willjschmitt/joulia-controller/update_test.py

"""Tests for the update module."""

import unittest

from testing.stub_joulia_webserver_client import StubJouliaHTTPClient
from update import GitUpdateManager


class StubRepo(object):
    """Stub object for a gitpython Repo object."""
    def __init__(self):
        self.head = StubHead()
        self.remotes = StubRemotes()
        self.git = StubGit()

    def commit(self, commit_hash):
        return StubCommit()


class StubHead(object):
    def __init__(self):
        self.object = StubObject()


class StubObject(object):
    def __init__(self):
        self.binsha = bytearray.fromhex('abcd'*10)


class StubRemotes(object):
    def __init__(self):
        self.origin = StubOrigin()


class StubOrigin(object):
    def fetch(self):
        pass


class StubCommit(object):
    pass


class StubGit(object):
    def checkout(self, commit):
        pass


def stub_system_restarter():
    """Fake function that just returns nothing to act like a "system restarter".
    """


class TestGitUpdateManager(unittest.TestCase):
    def setUp(self):
        self.repo = StubRepo()
        self.client = StubJouliaHTTPClient("http://fakehost")
        self.client.brewhouse = {
            'id': 1,
            'software_version': 9,
        }
        self.brewhouse_id = 1
        self.update_manager = GitUpdateManager(
            self.repo, self.client, self.brewhouse_id,
            system_restarter=stub_system_restarter)

    def test_check_version_no_new_version(self):
        self.client.latest_controller_release = {
            "id": 9,
            "commit_hash": "abcdabcdabcdabcdabcdabcdabcdabcdabcdabcd"}
        updated = self.update_manager._check_version()
        self.assertFalse(updated)

    def test_check_version_no_new_version_wrong_saved_id(self):
        self.client.latest_controller_release = {
            "id": 10,
            "commit_hash": "abcdabcdabcdabcdabcdabcdabcdabcdabcdabcd"}
        updated = self.update_manager._check_version()
        self.assertTrue(updated)
        self.assertEqual(self.client.updated_brewhouse, {
            'id': 1,
            'software_version': 10,
        })

    def test_check_version_no_version(self):
        self.client.latest_controller_release = {
            "id": 10,
            "commit_hash": None}
        updated = self.update_manager._check_version()
        self.assertFalse(updated)

    def test_check_version_new_version(self):
        self.client.latest_controller_release = {
            "id": 10,
            "commit_hash": "dcbadcbadcbadcbadcbadcbadcbadcbadcbadcba"}
        updated = self.update_manager._check_version()
        self.assertTrue(updated)

    def test_check_version_updates_server(self):
        self.assertIsNone(self.client.updated_brewhouse)
        self.client.latest_controller_release = {
            "id": 10,
            "commit_hash": "dcbadcbadcbadcbadcbadcbadcbadcbadcbadcba"}
        updated = self.update_manager._check_version()
        self.assertTrue(updated)
        self.assertEqual(self.client.updated_brewhouse, {
            'id': 1,
            'software_version': 10,
        })
